sggrissom/turn-taker/enclosure-redesign/output/preview_base.png

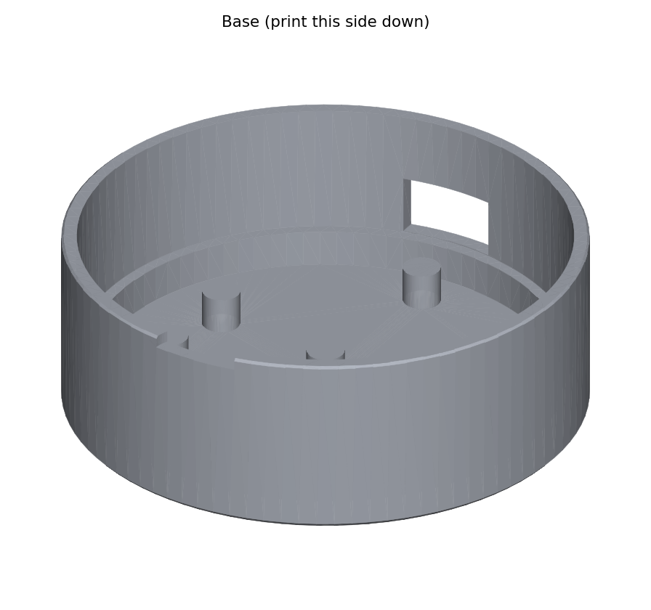
enclosure-redesign/output/preview_base.png
