sggrissom/turn-taker/enclosure-redesign/output/preview_exploded.png

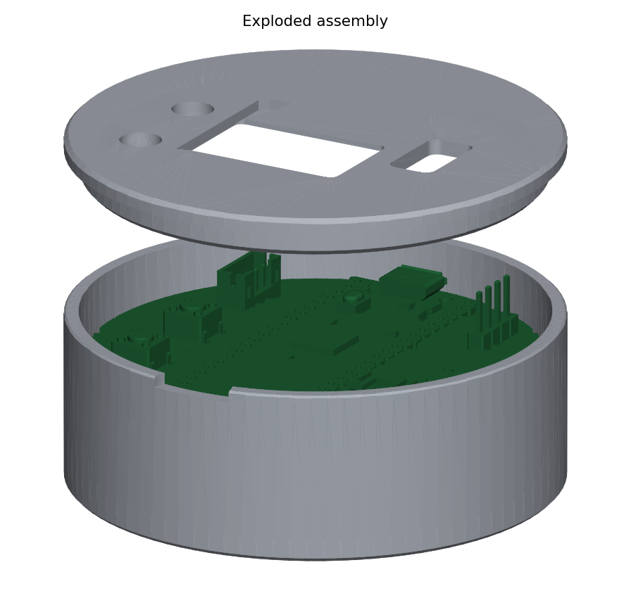
enclosure-redesign/output/preview_exploded.png
