sggrissom/turn-taker/enclosure-redesign/output/preview_lid_bottom.png

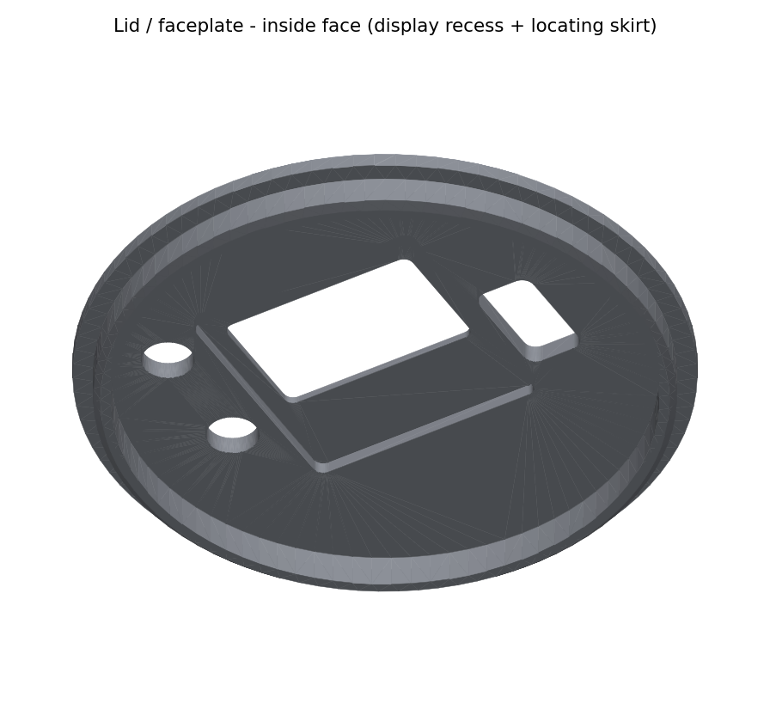
enclosure-redesign/output/preview_lid_bottom.png
