sggrissom/turn-taker/enclosure-redesign/output/preview_lid_top.png

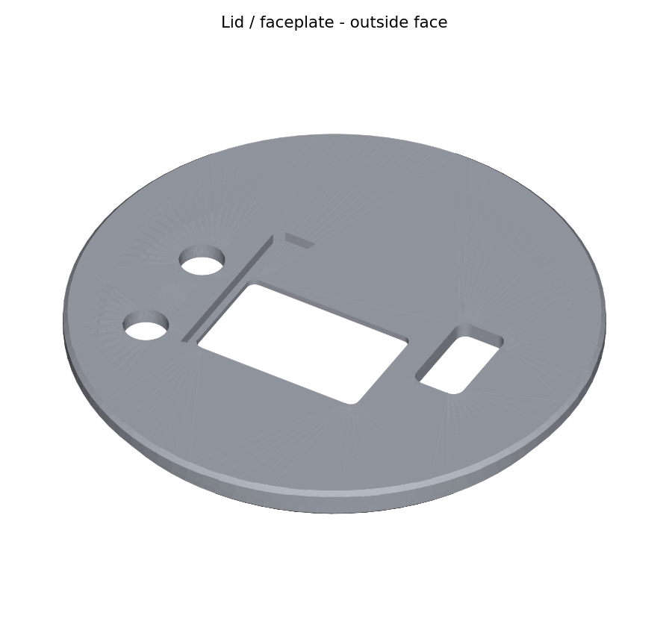
enclosure-redesign/output/preview_lid_top.png
