sggrissom/turn-taker/enclosure-redesign/output/preview_pcb_in_base.png

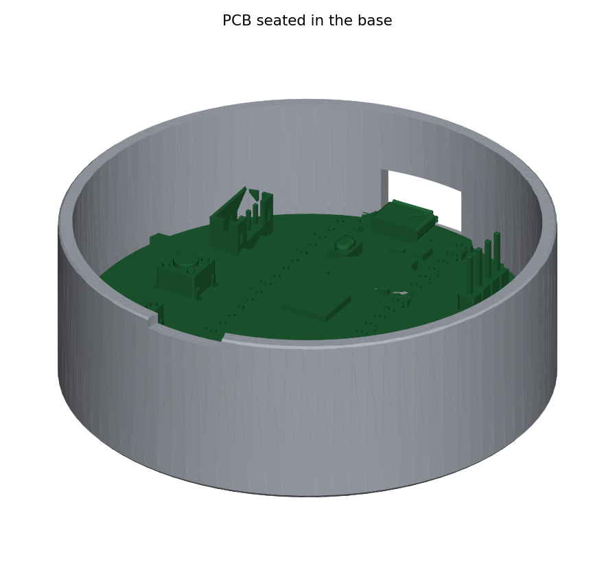
enclosure-redesign/output/preview_pcb_in_base.png
