sggrissom/turn-taker/enclosure-redesign/output/preview_section.png

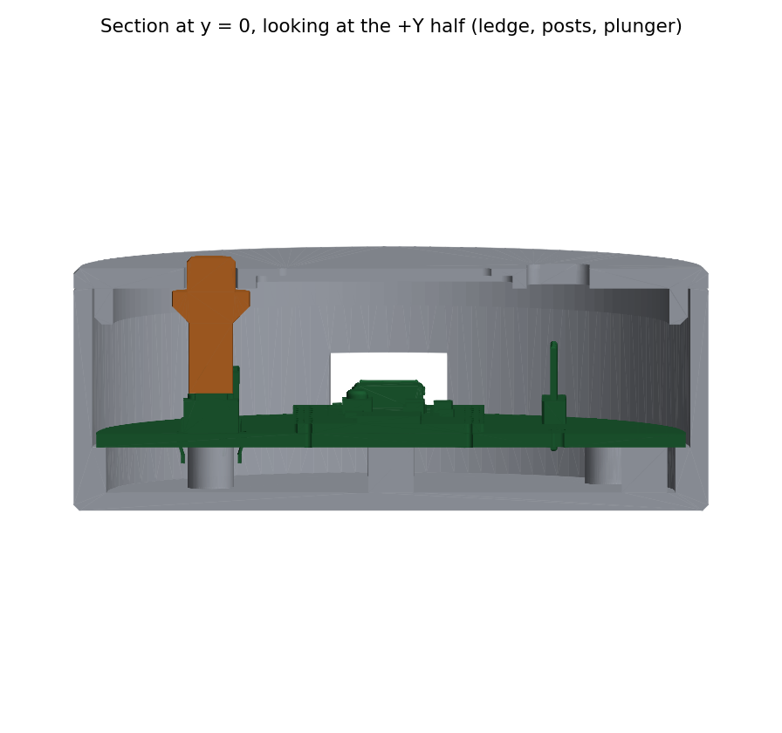
enclosure-redesign/output/preview_section.png
