sggrissom/turn-taker/enclosure-redesign/output/preview_top.png

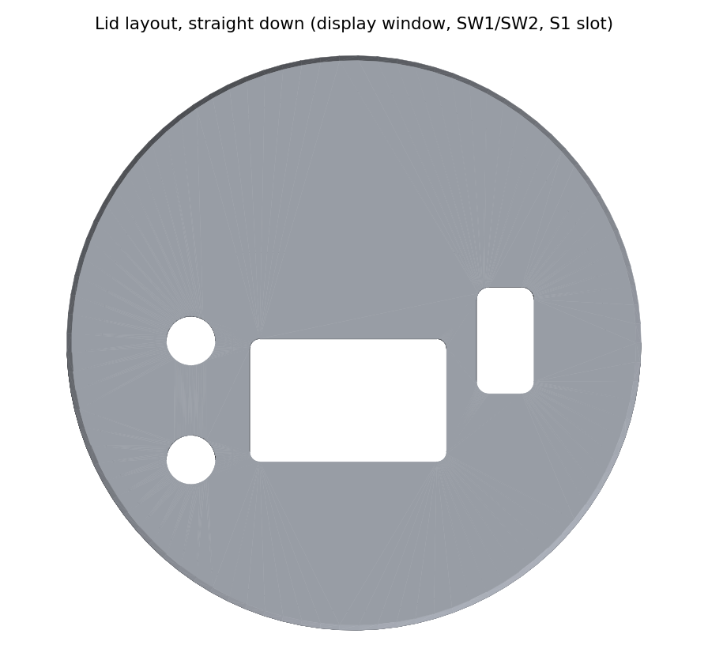
enclosure-redesign/output/preview_top.png
