sggrissom/turn-taker/enclosure-redesign/output/preview_assembled.png

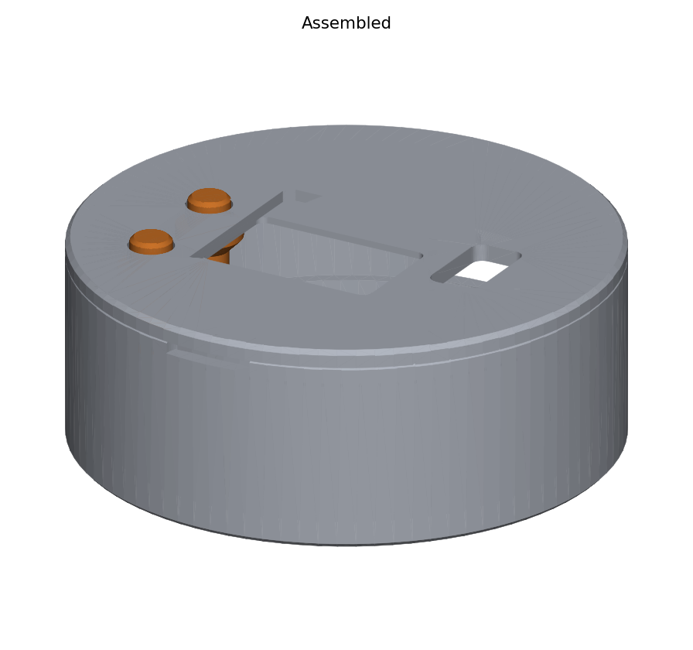
enclosure-redesign/output/preview_assembled.png
